bigcrimping/submerge/code/bouy_code/wave_array.h

float wave_array[]= {0, 0.12, 0.238, 0.352, 0.462, 0.565, 0.659, 0.745, 0.819, 0.877, 0.921, 0.952, 0.976, 0.991, 0.999, 0.999, 0.99, 0.974, 0.949, 0.917, 0.878, 0.831, 0.778, 0.711, 0.63, 0.533, 0.427, 0.316, 0.2, 0.082, -0.038, -0.148, -0.246, -0.332, -0.406, -0.469, -0.521, -0.563, -0.604, -0.643, -0.68, -0.716, -0.75, -0.782, -0.812, -0.841, -0.867, -0.89, -0.912, -0.931, -0.948, -0.963, -0.975, -0.985, -0.993, -0.997, -1, -1, -0.997, -0.992, -0.984, -0.974, -0.962, -0.947, -0.93, -0.91, -0.888, -0.864, -0.838, -0.809, -0.779, -0.747, -0.713, -0.677, -0.639, -0.6, -0.559, -0.517, -0.473, -0.42, -0.355, -0.279, -0.192, -0.093, 0.017};
